Nadeera3784/kepler_fw/Hardware/images/call_from.jpg

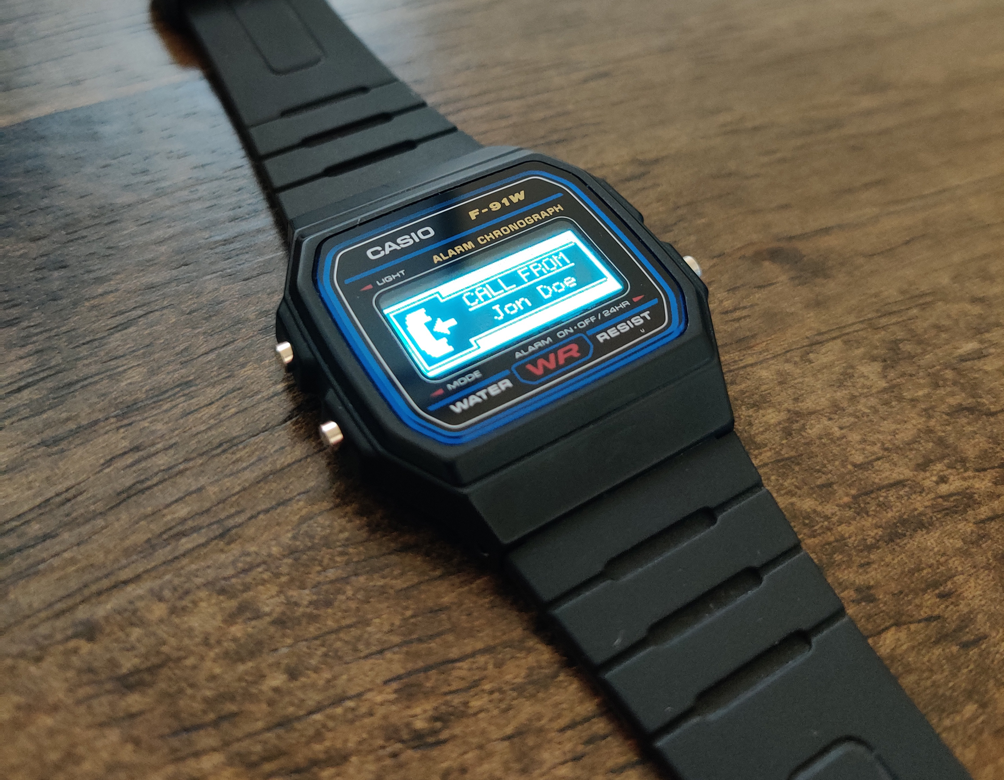
Hardware/images/call_from.jpg
